ADBeta/00314S2D-ASCII_Display_Module/Images/ASCII-Table.png

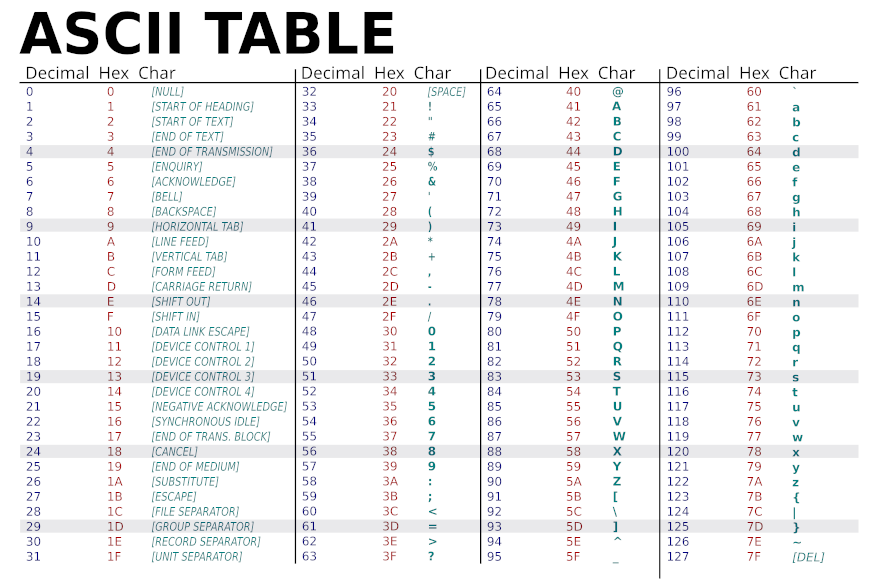
Images/ASCII-Table.png
