ADBeta/00314S2D-ASCII_Display_Module/Tools/starburst-font-designer/assets/all-dim.png

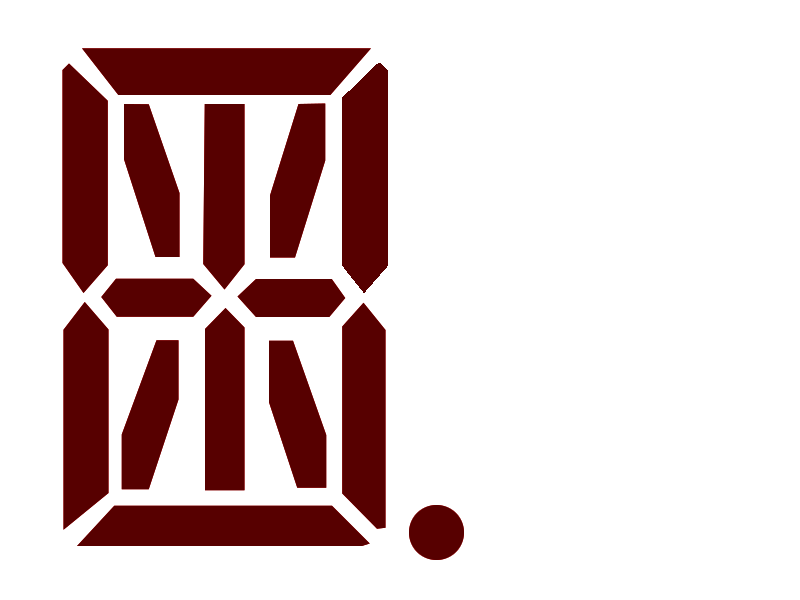
Tools/starburst-font-designer/assets/all-dim.png
