ADBeta/00314S2D-ASCII_Display_Module/Tools/starburst-font-designer/assets/c-lit.png

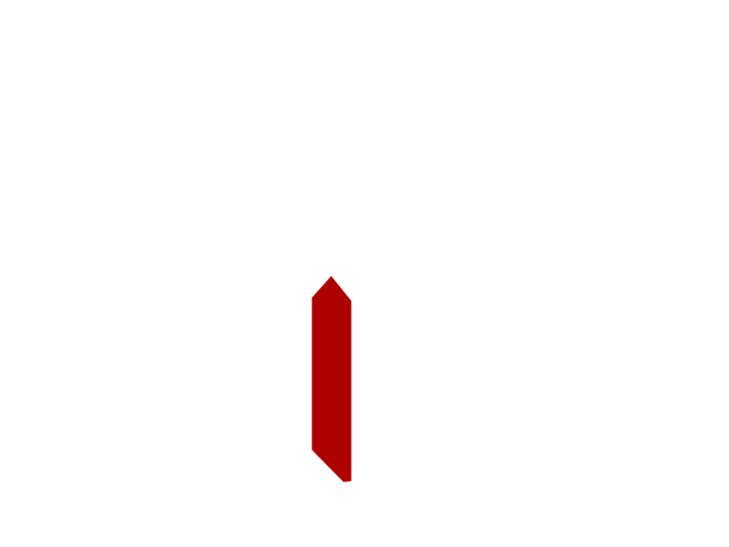
Tools/starburst-font-designer/assets/c-lit.png
