ADBeta/00314S2D-ASCII_Display_Module/Tools/starburst-font-designer/assets/g2-lit.png

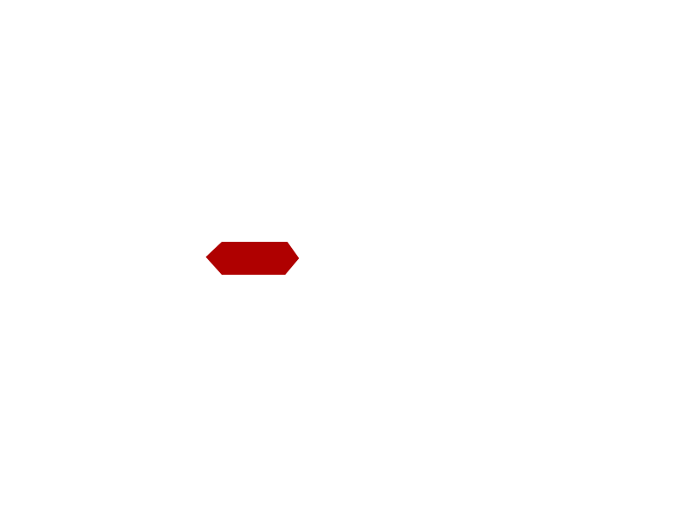
Tools/starburst-font-designer/assets/g2-lit.png
