ADBeta/00314S2D-ASCII_Display_Module/Firmware/MkI/src/lib_uart.h

/******************************************************************************
* This is a modified version of lib_uart, to remove the ring buffer,
* and incorperate the ISR into main.c
*
* lib_uart - A simple but full-featured library for UART on the CH32V003
*
* See GitHub for more information: 
* https://github.com/ADBeta/CH32V003_lib_uart
* 
* 23 Sep 2024    Version 5.3
*
* Released under the MIT Licence
* Copyright ADBeta (c) 2024
*
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
* THE SOFTWARE IS PROVIDED "AS IS", WITHOUT WARRANTY OF ANY KIND, 
* EXPRESS OR IMPLIED, INCLUDING BUT NOT LIMITED TO THE WARRANTIES OF 
* MERCHANTABILITY, FITNESS FOR A PARTICULAR PURPOSE AND NONINFRINGEMENT.
* IN NO EVENT SHALL THE AUTHORS OR COPYRIGHT HOLDERS BE LIABLE FOR ANY CLAIM,
* DAMAGES OR OTHER LIABILITY, WHETHER IN AN ACTION OF CONTRACT, TORT OR 
* OTHERWISE, ARISING FROM, OUT OF OR IN CONNECTION WITH THE SOFTWARE OR THE 
* USE OR OTHER DEALINGS IN THE SOFTWARE.
******************************************************************************/
#ifndef LIB_UART_H
#define LIB_UART_H

#include "ch32v003fun.h"
#include <stddef.h>
#include <stdbool.h>

/*** Configuration Flags *****************************************************/
/*
Set these flags in funconfig.h. 

Enable/Disable overwriting of the RX Ring Buffer.
Enabled:  Incomming data will overwrite older data in the buffer
Disabled: Incomming data will not be added to the buffer until space is free
  
#define RX_RING_BUFFER_OVERWRITE

NOTE: UART_ALTERNATE_1 will disable SWIO (PD1)

Pinout        TX        RX        CTS        RTS
Default       PD5       PD6       PD3        PC2
Alternate 1   PD0       PD1       PC3        PC2
Alternate 2   PD6       PD5       PC6        PC7
Alternate 3   PC0       PC1       PC6        PC7

#define UART_PINOUT_DEFAULT
#define UART_PINOUT_ALTERNATE_1
#define UART_PINOUT_ALTERNATE_2
#define UART_PINOUT_ALTERNATE_3
*/

/*** Macro Functions *********************************************************/
// DIV  = round( (HCLK / (16 * BAUD)) * 16 )
// Simplify equation and add Divisor/2 to simulate intager rounding
#define UART_CALC_DIV(BAUD) (((FUNCONF_SYSTEM_CORE_CLOCK) + ((BAUD) / 2)) / (BAUD))

// BAUD = round( (HCLK / (DIV / 16)) / 16 )
// Simplify equation and add Divisor/2 to simulate intager rounding
#define UART_CALC_BAUD(DIV) (((FUNCONF_SYSTEM_CORE_CLOCK) + ((DIV) / 2)) / (DIV))


/*** Typedefs and defines  ***************************************************/
// UART AFIO Reset Mask
#define UART_AFIO_RESET_MASK ((uint32_t)0xFFDFFFFB)

// Guard against no UART_PINOUT being defined. Default to _DEFAULT
#if !defined(UART_PINOUT_DEFAULT)     && \
    !defined(UART_PINOUT_ALTERNATE_1) && \
    !defined(UART_PINOUT_ALTERNATE_2) && \
    !defined(UART_PINOUT_ALTERNATE_3)

	#define UART_PINOUT_DEFAULT
#endif

// Default Pinout
// TX        RX        CTS        RTS
// PD5       PD6       PD3        PC2
#ifdef UART_PINOUT_DEFAULT
	#define UART_AFIO_MASK       ((uint32_t)0x00000000)
	//
	#define UART_TXRX_PORT_RCC   RCC_APB2Periph_GPIOD
	#define UART_CTS_PORT_RCC    RCC_APB2Periph_GPIOD
	#define UART_RTS_PORT_RCC    RCC_APB2Periph_GPIOC
	//
	#define UART_TXRX_PORT       GPIOD
	#define UART_CTS_PORT        GPIOD
	#define UART_RTS_PORT        GPIOC
	//
	#define UART_PIN_TX     5
	#define UART_PIN_RX     6
	#define UART_PIN_CTS    3
	#define UART_PIN_RTS    2
#endif

// Alternate Pinout 1
// This will Disable SWIO (PD1)
// TX        RX        CTS        RTS
// PD0       PD1       PC3        PC2
#ifdef UART_PINOUT_ALTERNATE_1
	#define UART_AFIO_MASK       ((uint32_t)0x04000004)
	//
	#define UART_TXRX_PORT_RCC   RCC_APB2Periph_GPIOD
	#define UART_CTS_PORT_RCC    RCC_APB2Periph_GPIOC
	#define UART_RTS_PORT_RCC    RCC_APB2Periph_GPIOC
	//
	#define UART_TXRX_PORT       GPIOD
	#define UART_CTS_PORT        GPIOC
	#define UART_RTS_PORT        GPIOC
	//
	#define UART_PIN_TX     0
	#define UART_PIN_RX     1
	#define UART_PIN_CTS    3
	#define UART_PIN_RTS    2
#endif

// Alternate Pinout 2
// TX        RX        CTS        RTS
// PD6       PD5       PC6        PC7
#ifdef UART_PINOUT_ALTERNATE_2
	#define UART_AFIO_MASK       ((uint32_t)0x00200000)
	//
	#define UART_TXRX_PORT_RCC   RCC_APB2Periph_GPIOD
	#define UART_CTS_PORT_RCC    RCC_APB2Periph_GPIOC
	#define UART_RTS_PORT_RCC    RCC_APB2Periph_GPIOC
	//
	#define UART_TXRX_PORT       GPIOD
	#define UART_CTS_PORT        GPIOC
	#define UART_RTS_PORT        GPIOC
	//
	#define UART_PIN_TX     6
	#define UART_PIN_RX     5
	#define UART_PIN_CTS    6
	#define UART_PIN_RTS    7
#endif

// Alternate Pinout 3
// TX        RX        CTS        RTS
// PC0       PC1       PC6        PC7
#ifdef UART_PINOUT_ALTERNATE_3
	#define UART_AFIO_MASK       ((uint32_t)0x00200004)
	//
	#define UART_TXRX_PORT_RCC   RCC_APB2Periph_GPIOC
	#define UART_CTS_PORT_RCC    RCC_APB2Periph_GPIOC
	#define UART_RTS_PORT_RCC    RCC_APB2Periph_GPIOC
	//
	#define UART_TXRX_PORT       GPIOC
	#define UART_CTS_PORT        GPIOC
	#define UART_RTS_PORT        GPIOC
	//
	#define UART_PIN_TX     0
	#define UART_PIN_RX     1
	#define UART_PIN_CTS    6
	#define UART_PIN_RTS    7
#endif


/// @brief UART Error Values
typedef enum {
	UART_OK              = 0,
	UART_INVALID_ARGS,
	UART_NOT_INITIALIZED,
	UART_TIMEOUT,
	UART_BUFFER_EMPTY,
} uart_err_t;


/// @brief Defines some commonly used baud rates 
typedef enum {                                               // Actual    Delta %
	UART_BAUD_921600 = ((uint16_t)UART_CALC_DIV(921600)),    // 923076    0.16% Fast
	UART_BAUD_460800 = ((uint16_t)UART_CALC_DIV(460800)),    // 461538    0.16% Fast
	UART_BAUD_230400 = ((uint16_t)UART_CALC_DIV(230400)),    // 230769    0.16% Fast
	UART_BAUD_115200 = ((uint16_t)UART_CALC_DIV(115200)),    // 115107    0.08% Slow
	UART_BAUD_57600  = ((uint16_t)UART_CALC_DIV(57600)),     // 57623     0.04% Fast
	UART_BAUD_38400  = ((uint16_t)UART_CALC_DIV(38400)),     // 38400     0.00% 
	UART_BAUD_19200  = ((uint16_t)UART_CALC_DIV(19200)),     // 19200     0.00%
	UART_BAUD_9600   = ((uint16_t)UART_CALC_DIV(9600)),      // 9600      0.00%
	UART_BAUD_4800   = ((uint16_t)UART_CALC_DIV(4800)),      // 4800      0.00%
	UART_BAUD_2400   = ((uint16_t)UART_CALC_DIV(2400)),      // 2400      0.00%
	UART_BAUD_1200   = ((uint16_t)UART_CALC_DIV(1200)),      // 1200      0.00%
} uart_baudrate_t;


/// @brief UART Word Length Enum
typedef enum {
	UART_WORDLENGTH_8 = ((uint16_t)0x0000),
	UART_WORDLENGTH_9 = ((uint16_t)0x1000),
} uart_wordlength_t;


/// @brief UART Parity Enum
typedef enum {
	UART_PARITY_NONE = ((uint16_t)0x0000),
	UART_PARITY_EVEN = ((uint16_t)0x0400),
	UART_PARITY_ODD  = ((uint16_t)0x0600),
} uart_parity_t;


/// @brief UART Stop Bits Enum
typedef enum {
	UART_STOPBITS_ONE       = ((uint16_t)0x0000),
	UART_STOPBITS_HALF      = ((uint16_t)0x1000),
	UART_STOPBITS_TWO       = ((uint16_t)0x2000),
	UART_STOPBITS_ONE_HALF  = ((uint16_t)0x3000),
} uart_stopbits_t;

/// @brief UART Flow Control Masks
typedef enum {
	UART_FLOWCTRL_NONE      = ((uint16_t)0x0000),
	UART_FLOWCTRL_CTS       = ((uint16_t)0x0200),
	UART_FLOWCTRL_RTS       = ((uint16_t)0x0100),
	UART_FLOWCTRL_CTS_RTS   = ((uint16_t)0x0300)

} uart_flowctrl_t;


/// @brief UART Configuration Struct
// TODO: Break bit?
typedef struct {
	uart_baudrate_t    baudrate;
	uart_wordlength_t  wordlength;
	uart_parity_t      parity;
	uart_stopbits_t    stopbits;
	uart_flowctrl_t    flowctrl;
} uart_config_t;


/*** Initialisers ************************************************************/
/// @brief Initiliase the UART peripheral with the passed configuratiion.
/// @param uart_config_t, UART configuration
/// @return uart_err_t, UART_NOT_INITIALIZED on error
uart_err_t uart_init(const uart_config_t *conf);


/*** Write *******************************************************************/
/// @brief writes raw bytes to the UART
/// @param buffer, raw buffer, can be any type
/// @param size, number of bytes to transmit.
/// @return uart_err_t status
uart_err_t uart_write(const void *buffer, size_t size);

/// @brief Prints a string to the UART, without any added ternination
/// @param string, input c string to print
/// @return uart_err_t status
uart_err_t uart_print(const char *string);

/// @brief Prints a string to the UART, and adds termination \r\n characters
/// @param string, input c string to print
/// @return uart_err_t status
uart_err_t uart_println(const char *string);

#endif
